ArpanHalder/TeleMonitor/documentation/Companies that have taken Model Based Approach.PNG

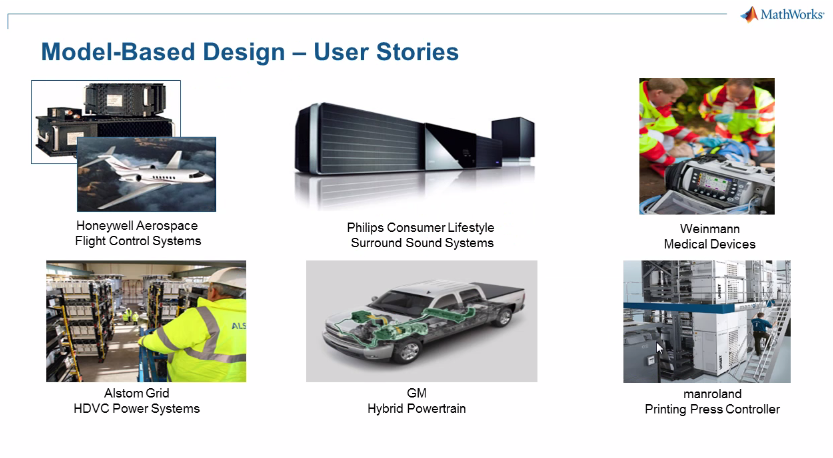
documentation/Companies that have taken Model Based Approach.PNG
