ArpanHalder/TeleMonitor/documentation/PCB TeleMonitor V1.png

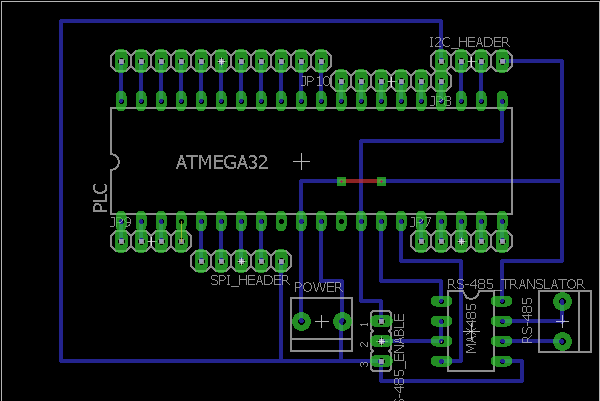
documentation/PCB TeleMonitor V1.png
