ArpanHalder/TeleMonitor/documentation/TeleMonitorProtocol.PNG

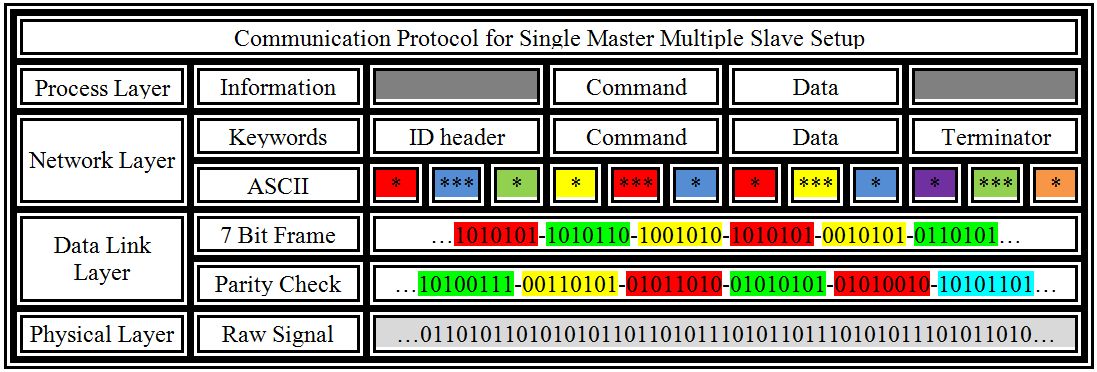
documentation/TeleMonitorProtocol.PNG
